alinxalinx/AX7Z020B_2023.1/RSTdocxs/7Z020B_S2_RSTdocument_CN/images/19_media/image26.png

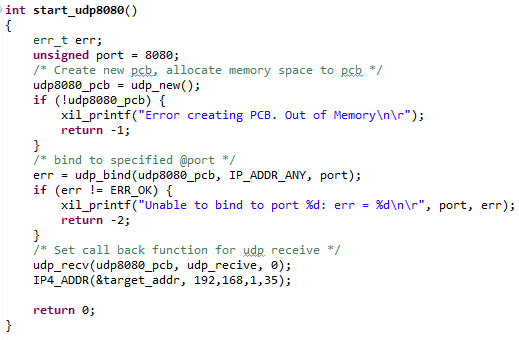
RSTdocxs/7Z020B_S2_RSTdocument_CN/images/19_media/image26.png
