alinxalinx/AX7Z020B_2023.1/RSTdocxs/7Z020B_S3_RSTdocument_CN/images/images0/image1.png

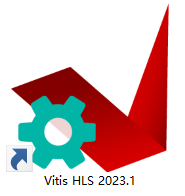
RSTdocxs/7Z020B_S3_RSTdocument_CN/images/images0/image1.png
