alinxalinx/AX7Z020B_2023.1/RSTdocxs/7Z020B_S3_RSTdocument_CN/images/images1/image44.png

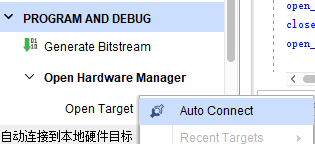
RSTdocxs/7Z020B_S3_RSTdocument_CN/images/images1/image44.png
