alinxalinx/AX7Z020B_2023.1/RSTdocxs/7Z020B_S3_RSTdocument_CN/images/images3/image51.png

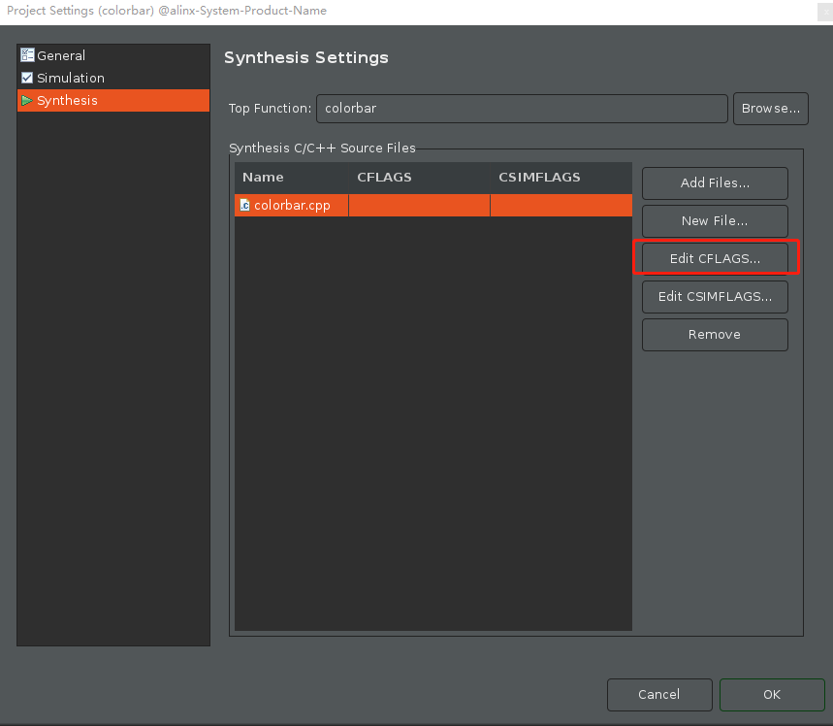
RSTdocxs/7Z020B_S3_RSTdocument_CN/images/images3/image51.png
