alinxalinx/AX7Z020B_2023.1/RSTdocxs/7Z020B_S4_RSTdocument_CN/images/11_media/image39.png

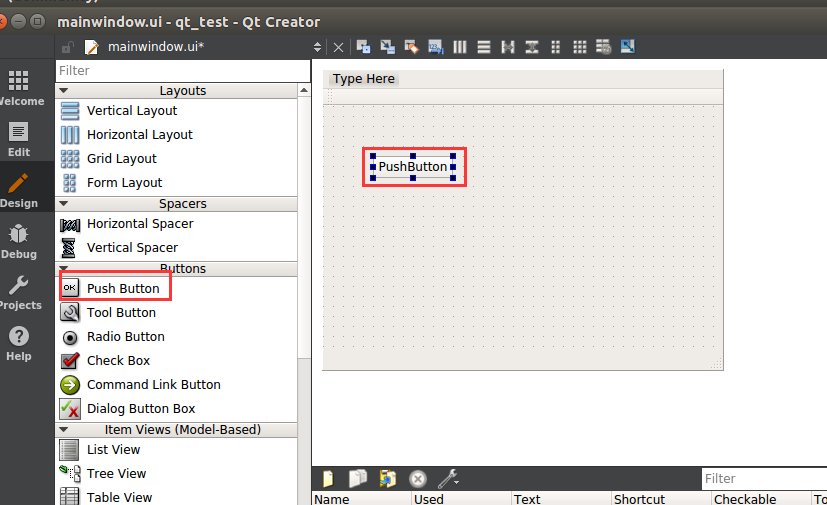
RSTdocxs/7Z020B_S4_RSTdocument_CN/images/11_media/image39.png
