alinxalinx/AX7Z020B_2023.1/course_s4_linux/14_lcd_touch/lcd_touch/Vivado/auto_create_project/src/constraints/lcd7.xdc

set_property PACKAGE_PIN M18 [get_ports lcd_intr]
set_property PACKAGE_PIN M17 [get_ports {lcd_bl_pwm[0]}]
set_property PACKAGE_PIN K19 [get_ports lcd_i2c_scl_io]
set_property PACKAGE_PIN J19 [get_ports lcd_i2c_sda_io]
set_property PACKAGE_PIN B19 [get_ports lcd_hsync]
set_property PACKAGE_PIN A20 [get_ports lcd_vsync]
set_property PACKAGE_PIN B20 [get_ports lcd_dclk]
set_property PACKAGE_PIN C20 [get_ports lcd_de]
set_property PACKAGE_PIN G19 [get_ports {lcd_data[6]}]
set_property PACKAGE_PIN G20 [get_ports {lcd_data[7]}]
set_property PACKAGE_PIN M19 [get_ports {lcd_data[4]}]
set_property PACKAGE_PIN M20 [get_ports {lcd_data[5]}]
set_property PACKAGE_PIN D20 [get_ports {lcd_data[2]}]
set_property PACKAGE_PIN D19 [get_ports {lcd_data[3]}]
set_property PACKAGE_PIN L20 [get_ports {lcd_data[0]}]
set_property PACKAGE_PIN L19 [get_ports {lcd_data[1]}]
set_property PACKAGE_PIN F16 [get_ports {lcd_data[14]}]
set_property PACKAGE_PIN F17 [get_ports {lcd_data[15]}]
set_property PACKAGE_PIN H20 [get_ports {lcd_data[12]}]
set_property PACKAGE_PIN J20 [get_ports {lcd_data[13]}]
set_property PACKAGE_PIN G18 [get_ports {lcd_data[10]}]
set_property PACKAGE_PIN G17 [get_ports {lcd_data[11]}]
set_property PACKAGE_PIN H17 [get_ports {lcd_data[8]}]
set_property PACKAGE_PIN H16 [get_ports {lcd_data[9]}]
set_property PACKAGE_PIN G15 [get_ports {lcd_data[22]}]
set_property PACKAGE_PIN H15 [get_ports {lcd_data[23]}]
set_property PACKAGE_PIN K18 [get_ports {lcd_data[20]}]
set_property PACKAGE_PIN K17 [get_ports {lcd_data[21]}]
set_property PACKAGE_PIN J16 [get_ports {lcd_data[18]}]
set_property PACKAGE_PIN K16 [get_ports {lcd_data[19]}]
set_property PACKAGE_PIN N16 [get_ports {lcd_data[16]}]
set_property PACKAGE_PIN N15 [get_ports {lcd_data[17]}]

set_property IOSTANDARD LVCMOS33 [get_ports lcd_intr]
set_property IOSTANDARD LVCMOS33 [get_ports {lcd_bl_pwm[0]}]
set_property IOSTANDARD LVCMOS33 [get_ports lcd_i2c_scl_io]
set_property IOSTANDARD LVCMOS33 [get_ports lcd_i2c_sda_io]
set_property IOSTANDARD LVCMOS33 [get_ports lcd_hsync]
set_property IOSTANDARD LVCMOS33 [get_ports lcd_vsync]
set_property IOSTANDARD LVCMOS33 [get_ports lcd_dclk]
set_property IOSTANDARD LVCMOS33 [get_ports lcd_de]
set_property IOSTANDARD LVCMOS33 [get_ports {lcd_data[6]}]
set_property IOSTANDARD LVCMOS33 [get_ports {lcd_data[7]}]
set_property IOSTANDARD LVCMOS33 [get_ports {lcd_data[4]}]
set_property IOSTANDARD LVCMOS33 [get_ports {lcd_data[5]}]
set_property IOSTANDARD LVCMOS33 [get_ports {lcd_data[2]}]
set_property IOSTANDARD LVCMOS33 [get_ports {lcd_data[3]}]
set_property IOSTANDARD LVCMOS33 [get_ports {lcd_data[0]}]
set_property IOSTANDARD LVCMOS33 [get_ports {lcd_data[1]}]
set_property IOSTANDARD LVCMOS33 [get_ports {lcd_data[14]}]
set_property IOSTANDARD LVCMOS33 [get_ports {lcd_data[15]}]
set_property IOSTANDARD LVCMOS33 [get_ports {lcd_data[12]}]
set_property IOSTANDARD LVCMOS33 [get_ports {lcd_data[13]}]
set_property IOSTANDARD LVCMOS33 [get_ports {lcd_data[10]}]
set_property IOSTANDARD LVCMOS33 [get_ports {lcd_data[11]}]
set_property IOSTANDARD LVCMOS33 [get_ports {lcd_data[8]}]
set_property IOSTANDARD LVCMOS33 [get_ports {lcd_data[9]}]
set_property IOSTANDARD LVCMOS33 [get_ports {lcd_data[22]}]
set_property IOSTANDARD LVCMOS33 [get_ports {lcd_data[23]}]
set_property IOSTANDARD LVCMOS33 [get_ports {lcd_data[20]}]
set_property IOSTANDARD LVCMOS33 [get_ports {lcd_data[21]}]
set_property IOSTANDARD LVCMOS33 [get_ports {lcd_data[18]}]
set_property IOSTANDARD LVCMOS33 [get_ports {lcd_data[19]}]
set_property IOSTANDARD LVCMOS33 [get_ports {lcd_data[16]}]
set_property IOSTANDARD LVCMOS33 [get_ports {lcd_data[17]}]

set_property PULLUP true [get_ports lcd_i2c_scl_io]
set_property PULLUP true [get_ports lcd_i2c_sda_io]

set_property DRIVE 16 [get_ports {lcd_data[23]}]
set_property DRIVE 16 [get_ports {lcd_data[22]}]
set_property DRIVE 16 [get_ports {lcd_data[21]}]
set_property DRIVE 16 [get_ports {lcd_data[20]}]
set_property DRIVE 16 [get_ports {lcd_data[19]}]
set_property DRIVE 16 [get_ports {lcd_data[18]}]
set_property DRIVE 16 [get_ports {lcd_data[17]}]
set_property DRIVE 16 [get_ports {lcd_data[16]}]
set_property DRIVE 16 [get_ports {lcd_data[15]}]
set_property DRIVE 16 [get_ports {lcd_data[14]}]
set_property DRIVE 16 [get_ports {lcd_data[13]}]
set_property DRIVE 16 [get_ports {lcd_data[12]}]
set_property DRIVE 16 [get_ports {lcd_data[11]}]
set_property DRIVE 16 [get_ports {lcd_data[10]}]
set_property DRIVE 16 [get_ports {lcd_data[9]}]
set_property DRIVE 16 [get_ports {lcd_data[8]}]
set_property DRIVE 16 [get_ports {lcd_data[7]}]
set_property DRIVE 16 [get_ports {lcd_data[6]}]
set_property DRIVE 16 [get_ports {lcd_data[5]}]
set_property DRIVE 16 [get_ports {lcd_data[4]}]
set_property DRIVE 16 [get_ports {lcd_data[3]}]
set_property DRIVE 16 [get_ports {lcd_data[2]}]
set_property DRIVE 16 [get_ports {lcd_data[1]}]
set_property DRIVE 16 [get_ports {lcd_data[0]}]
set_property SLEW FAST [get_ports {lcd_data[23]}]
set_property SLEW FAST [get_ports {lcd_data[22]}]
set_property SLEW FAST [get_ports {lcd_data[21]}]
set_property SLEW FAST [get_ports {lcd_data[20]}]
set_property SLEW FAST [get_ports {lcd_data[19]}]
set_property SLEW FAST [get_ports {lcd_data[18]}]
set_property SLEW FAST [get_ports {lcd_data[17]}]
set_property SLEW FAST [get_ports {lcd_data[16]}]
set_property SLEW FAST [get_ports {lcd_data[15]}]
set_property SLEW FAST [get_ports {lcd_data[14]}]
set_property SLEW FAST [get_ports {lcd_data[13]}]
set_property SLEW FAST [get_ports {lcd_data[12]}]
set_property SLEW FAST [get_ports {lcd_data[11]}]
set_property SLEW FAST [get_ports {lcd_data[10]}]
set_property SLEW FAST [get_ports {lcd_data[9]}]
set_property SLEW FAST [get_ports {lcd_data[8]}]
set_property SLEW FAST [get_ports {lcd_data[7]}]
set_property SLEW FAST [get_ports {lcd_data[6]}]
set_property SLEW FAST [get_ports {lcd_data[5]}]
set_property SLEW FAST [get_ports {lcd_data[4]}]
set_property SLEW FAST [get_ports {lcd_data[3]}]
set_property SLEW FAST [get_ports {lcd_data[2]}]
set_property SLEW FAST [get_ports {lcd_data[1]}]
set_property SLEW FAST [get_ports {lcd_data[0]}]
set_property DRIVE 16 [get_ports lcd_de]
set_property DRIVE 16 [get_ports lcd_hsync]
set_property DRIVE 16 [get_ports lcd_vsync]
set_property DRIVE 16 [get_ports {lcd_bl_pwm[0]}]
set_property SLEW FAST [get_ports lcd_de]
set_property SLEW FAST [get_ports lcd_hsync]
set_property SLEW FAST [get_ports lcd_vsync]
set_property SLEW FAST [get_ports {lcd_bl_pwm[0]}]
set_property DRIVE 16 [get_ports lcd_dclk]
set_property SLEW FAST [get_ports lcd_dclk]
