alinxalinx/AX7Z020B_2023.1/course_s1_fpga/01_led/auto_create_project/src/constraints/led.xdc

set_property PACKAGE_PIN H18 [get_ports {led[3]}]
set_property PACKAGE_PIN J18 [get_ports {led[2]}]
set_property PACKAGE_PIN K14 [get_ports {led[1]}]
set_property PACKAGE_PIN J14 [get_ports {led[0]}]
set_property PACKAGE_PIN M15 [get_ports rst_n]
set_property PACKAGE_PIN U18 [get_ports sys_clk]
set_property IOSTANDARD LVCMOS33 [get_ports {led[3]}]
set_property IOSTANDARD LVCMOS33 [get_ports {led[2]}]
set_property IOSTANDARD LVCMOS33 [get_ports {led[1]}]
set_property IOSTANDARD LVCMOS33 [get_ports {led[0]}]
set_property IOSTANDARD LVCMOS33 [get_ports rst_n]
set_property IOSTANDARD LVCMOS33 [get_ports sys_clk]

create_clock -period 20.000 -name sys_clk -waveform {0.000 10.000} [get_ports sys_clk]

create_debug_core u_ila_0 ila
set_property ALL_PROBE_SAME_MU true [get_debug_cores u_ila_0]
set_property ALL_PROBE_SAME_MU_CNT 1 [get_debug_cores u_ila_0]
set_property C_ADV_TRIGGER false [get_debug_cores u_ila_0]
set_property C_DATA_DEPTH 1024 [get_debug_cores u_ila_0]
set_property C_EN_STRG_QUAL false [get_debug_cores u_ila_0]
set_property C_INPUT_PIPE_STAGES 0 [get_debug_cores u_ila_0]
set_property C_TRIGIN_EN false [get_debug_cores u_ila_0]
set_property C_TRIGOUT_EN false [get_debug_cores u_ila_0]
set_property port_width 1 [get_debug_ports u_ila_0/clk]
connect_debug_port u_ila_0/clk [get_nets [list sys_clk_IBUF_BUFG]]
set_property PROBE_TYPE DATA_AND_TRIGGER [get_debug_ports u_ila_0/probe0]
set_property port_width 4 [get_debug_ports u_ila_0/probe0]
connect_debug_port u_ila_0/probe0 [get_nets [list {led_OBUF[0]} {led_OBUF[1]} {led_OBUF[2]} {led_OBUF[3]}]]
create_debug_port u_ila_0 probe
set_property PROBE_TYPE DATA_AND_TRIGGER [get_debug_ports u_ila_0/probe1]
set_property port_width 32 [get_debug_ports u_ila_0/probe1]
connect_debug_port u_ila_0/probe1 [get_nets [list {timer_cnt[0]} {timer_cnt[1]} {timer_cnt[2]} {timer_cnt[3]} {timer_cnt[4]} {timer_cnt[5]} {timer_cnt[6]} {timer_cnt[7]} {timer_cnt[8]} {timer_cnt[9]} {timer_cnt[10]} {timer_cnt[11]} {timer_cnt[12]} {timer_cnt[13]} {timer_cnt[14]} {timer_cnt[15]} {timer_cnt[16]} {timer_cnt[17]} {timer_cnt[18]} {timer_cnt[19]} {timer_cnt[20]} {timer_cnt[21]} {timer_cnt[22]} {timer_cnt[23]} {timer_cnt[24]} {timer_cnt[25]} {timer_cnt[26]} {timer_cnt[27]} {timer_cnt[28]} {timer_cnt[29]} {timer_cnt[30]} {timer_cnt[31]}]]
set_property C_CLK_INPUT_FREQ_HZ 300000000 [get_debug_cores dbg_hub]
set_property C_ENABLE_CLK_DIVIDER false [get_debug_cores dbg_hub]
set_property C_USER_SCAN_CHAIN 1 [get_debug_cores dbg_hub]
connect_debug_port dbg_hub/clk [get_nets sys_clk_IBUF_BUFG]
