alinxalinx/AX7Z020B_2023.1/course_s2_vitis/14_ad7606_dma_hdmi/Vivado/auto_create_project/src/constraints/ad7606.xdc

set_property PACKAGE_PIN M18 [get_ports {ADC_PORT_ad7606_os[1]}]
set_property PACKAGE_PIN M17 [get_ports {ADC_PORT_ad7606_os[0]}]
set_property PACKAGE_PIN K19 [get_ports  ADC_PORT_ad7606_convstab]
set_property PACKAGE_PIN J19 [get_ports {ADC_PORT_ad7606_os[2]}]
set_property PACKAGE_PIN B19 [get_ports  ADC_PORT_ad7606_rd]
set_property PACKAGE_PIN A20 [get_ports  ADC_PORT_ad7606_reset]
set_property PACKAGE_PIN B20 [get_ports  ADC_PORT_ad7606_busy]
set_property PACKAGE_PIN C20 [get_ports  ADC_PORT_ad7606_cs]
set_property PACKAGE_PIN G20 [get_ports  ADC_PORT_ad7606_first_data]
set_property PACKAGE_PIN D20 [get_ports {ADC_PORT_ad7606_data[0]}]
set_property PACKAGE_PIN D19 [get_ports {ADC_PORT_ad7606_data[1]}]
set_property PACKAGE_PIN L20 [get_ports {ADC_PORT_ad7606_data[2]}]
set_property PACKAGE_PIN L19 [get_ports {ADC_PORT_ad7606_data[3]}]
set_property PACKAGE_PIN F16 [get_ports {ADC_PORT_ad7606_data[4]}]
set_property PACKAGE_PIN F17 [get_ports {ADC_PORT_ad7606_data[5]}]
set_property PACKAGE_PIN H20 [get_ports {ADC_PORT_ad7606_data[6]}]
set_property PACKAGE_PIN J20 [get_ports {ADC_PORT_ad7606_data[7]}]
set_property PACKAGE_PIN G18 [get_ports {ADC_PORT_ad7606_data[8]}]
set_property PACKAGE_PIN G17 [get_ports {ADC_PORT_ad7606_data[9]}]
set_property PACKAGE_PIN H17 [get_ports {ADC_PORT_ad7606_data[10]}]
set_property PACKAGE_PIN H16 [get_ports {ADC_PORT_ad7606_data[11]}]
set_property PACKAGE_PIN G15 [get_ports {ADC_PORT_ad7606_data[12]}]
set_property PACKAGE_PIN H15 [get_ports {ADC_PORT_ad7606_data[13]}]
set_property PACKAGE_PIN K18 [get_ports {ADC_PORT_ad7606_data[14]}]
set_property PACKAGE_PIN K17 [get_ports {ADC_PORT_ad7606_data[15]}]



set_property IOSTANDARD LVCMOS33 [get_ports ADC_PORT_ad7606_convstab]
set_property IOSTANDARD LVCMOS33 [get_ports ADC_PORT_ad7606_reset]
set_property IOSTANDARD LVCMOS33 [get_ports ADC_PORT_ad7606_rd]
set_property IOSTANDARD LVCMOS33 [get_ports ADC_PORT_ad7606_cs]
set_property IOSTANDARD LVCMOS33 [get_ports ADC_PORT_ad7606_busy]
set_property IOSTANDARD LVCMOS33 [get_ports ADC_PORT_ad7606_first_data]
set_property IOSTANDARD LVCMOS33 [get_ports {ADC_PORT_ad7606_os[*]}]
set_property IOSTANDARD LVCMOS33 [get_ports {ADC_PORT_ad7606_data[*]}]
