alinxalinx/AX7Z020B_2023.1/course_s2_vitis/12_ad9280_dma_hdmi/Vivado/auto_create_project/src/constraints/ad9280.xdc

set_property PACKAGE_PIN K18 [get_ports adc_clk]
set_property PACKAGE_PIN H20 [get_ports {adc_data[0]}]
set_property PACKAGE_PIN J20 [get_ports {adc_data[1]}]
set_property PACKAGE_PIN G18 [get_ports {adc_data[2]}]
set_property PACKAGE_PIN G17 [get_ports {adc_data[3]}]
set_property PACKAGE_PIN H17 [get_ports {adc_data[4]}]
set_property PACKAGE_PIN H16 [get_ports {adc_data[5]}]
set_property PACKAGE_PIN G15 [get_ports {adc_data[6]}]
set_property PACKAGE_PIN H15 [get_ports {adc_data[7]}]


set_property IOSTANDARD LVCMOS33 [get_ports adc_clk]
set_property IOSTANDARD LVCMOS33 [get_ports {adc_data[*]}]
