alinxalinx/AX7Z020B_2023.1/course_s2_vitis/22_an5641_mipi_hdmi/Vivado/auto_create_project/src/constraints/mipi.xdc

set_property PACKAGE_PIN U7 [get_ports {cam_gpio_tri_io[0]}]
set_property IOSTANDARD LVCMOS33 [get_ports {cam_gpio_tri_io[0]}]
set_property PULLUP true [get_ports {cam_gpio_tri_io[0]}]

set_property -dict {PACKAGE_PIN T5 IOSTANDARD LVCMOS33} [get_ports cam_i2c_scl_io]
set_property -dict {PACKAGE_PIN U5 IOSTANDARD LVCMOS33} [get_ports cam_i2c_sda_io]

set_property PULLUP true [get_ports cam_i2c_scl_io]
set_property PULLUP true [get_ports cam_i2c_sda_io]

set_property INTERNAL_VREF 0.6 [get_iobanks 13]

set_property -dict {PACKAGE_PIN W8 IOSTANDARD HSUL_12} [get_ports mipi_phy_if_clk_lp_n]
set_property -dict {PACKAGE_PIN V8 IOSTANDARD HSUL_12} [get_ports mipi_phy_if_clk_lp_p]

set_property -dict {PACKAGE_PIN U10 IOSTANDARD HSUL_12} [get_ports {mipi_phy_if_data_lp_n[0]}]
set_property -dict {PACKAGE_PIN T9 IOSTANDARD HSUL_12} [get_ports {mipi_phy_if_data_lp_p[0]}]
set_property -dict {PACKAGE_PIN Y13 IOSTANDARD HSUL_12} [get_ports {mipi_phy_if_data_lp_n[1]}]
set_property -dict {PACKAGE_PIN Y12 IOSTANDARD HSUL_12} [get_ports {mipi_phy_if_data_lp_p[1]}]

set_property -dict {PACKAGE_PIN Y6 IOSTANDARD LVDS_25} [get_ports mipi_phy_if_clk_hs_n]
set_property -dict {PACKAGE_PIN Y7 IOSTANDARD LVDS_25} [get_ports mipi_phy_if_clk_hs_p]


set_property -dict {PACKAGE_PIN Y11 IOSTANDARD LVDS_25} [get_ports {mipi_phy_if_data_hs_n[0]}]
set_property -dict {PACKAGE_PIN W11 IOSTANDARD LVDS_25} [get_ports {mipi_phy_if_data_hs_p[0]}]
set_property -dict {PACKAGE_PIN U8 IOSTANDARD LVDS_25} [get_ports {mipi_phy_if_data_hs_n[1]}]
set_property -dict {PACKAGE_PIN U9 IOSTANDARD LVDS_25} [get_ports {mipi_phy_if_data_hs_p[1]}]
