alinxalinx/AX7Z020B_2023.1/course_s2_vitis/02_ps_xadc/Vivado/auto_create_project/src/constraints/xadc.xdc

set_property PACKAGE_PIN E17 [get_ports Vaux1_v_p]
set_property IOSTANDARD LVCMOS33 [get_ports Vaux1_v_n]
set_property IOSTANDARD LVCMOS33 [get_ports Vaux1_v_p]
set_property IOSTANDARD LVCMOS33 [get_ports Vaux9_v_n]
set_property IOSTANDARD LVCMOS33 [get_ports Vaux9_v_p]
set_property IOSTANDARD LVCMOS33 [get_ports Vaux12_v_n]
set_property IOSTANDARD LVCMOS33 [get_ports Vaux12_v_p]
