alinxalinx/AX7Z020B_2023.1/course_s2_vitis/08_dualcore_amp/Vivado/auto_create_project/src/constraints/led.xdc

#LED2
set_property IOSTANDARD LVCMOS33 [get_ports {led_tri_o[0]}]
set_property PACKAGE_PIN K14 [get_ports {led_tri_o[0]}]
#KEY2
set_property IOSTANDARD LVCMOS33 [get_ports {key_tri_i[0]}]
set_property PACKAGE_PIN M14 [get_ports {key_tri_i[0]}]
#LED1
set_property IOSTANDARD LVCMOS33 [get_ports {GPIO_tri_io[0]}]
set_property PACKAGE_PIN J14 [get_ports {GPIO_tri_io[0]}]
#KEY1
set_property IOSTANDARD LVCMOS33 [get_ports {GPIO_tri_io[1]}]
set_property PACKAGE_PIN M15 [get_ports {GPIO_tri_io[1]}]
