alinxalinx/AX7Z020B_2023.1/course_s2_vitis/22_an5641_mipi_hdmi/Vivado/auto_create_project/src/constraints/system.xdc

set_property BITSTREAM.GENERAL.COMPRESS TRUE [current_design]

#LED
set_property IOSTANDARD LVCMOS33 [get_ports {leds_tri_o[0]}]
set_property PACKAGE_PIN J14 [get_ports {leds_tri_o[0]}]
set_property IOSTANDARD LVCMOS33 [get_ports {leds_tri_o[1]}]
set_property PACKAGE_PIN K14 [get_ports {leds_tri_o[1]}]
