alinxalinx/AX7Z020B_2023.1/course_s2_vitis/22_an5641_mipi_hdmi/Vitis/auto_create_vitis/src/mipi_hdmi/vdma.c

#include "xil_printf.h"
#include "vdma.h"

u32 vdma_version(XAxiVdma *Vdma) {
	return XAxiVdma_GetVersion(Vdma);
}

int vdma_read_start(XAxiVdma *Vdma) {
	int Status;

	// MM2S Startup
	Status = XAxiVdma_DmaStart(Vdma, XAXIVDMA_READ);
	if (Status != XST_SUCCESS)
	{
	   xil_printf("Start read transfer failed %d\n\r", Status);
	   return XST_FAILURE;
	}

	return XST_SUCCESS;
}


int vdma_read_stop(XAxiVdma *Vdma) {
	XAxiVdma_DmaStop(Vdma, XAXIVDMA_READ);
	return XST_SUCCESS;
}


int vdma_read_init(short DeviceID,short HoriSizeInput,short VertSizeInput,short Stride,unsigned int FrameStoreStartAddr)
{
	XAxiVdma Vdma;
	XAxiVdma_Config *Config;
	XAxiVdma_DmaSetup ReadCfg;
	int Status;


	Config = XAxiVdma_LookupConfig(DeviceID);
	if (NULL == Config) {
		xil_printf("XAxiVdma_LookupConfig failure\r\n");
		return XST_FAILURE;
	}

	Status = XAxiVdma_CfgInitialize(&Vdma, Config, Config->BaseAddress);
	if (Status != XST_SUCCESS) {
		xil_printf("XAxiVdma_CfgInitialize failure\r\n");
		return XST_FAILURE;
	}

	

	ReadCfg.EnableCircularBuf = 1;
	ReadCfg.EnableFrameCounter = 0;
	ReadCfg.FixedFrameStoreAddr = 0;

	ReadCfg.EnableSync = 1;
	ReadCfg.PointNum = 1;

	ReadCfg.FrameDelay = 0;

	ReadCfg.VertSizeInput = VertSizeInput;
	ReadCfg.HoriSizeInput = HoriSizeInput;
	ReadCfg.Stride = Stride;

	Status = XAxiVdma_DmaConfig(&Vdma, XAXIVDMA_READ, &ReadCfg);
	if (Status != XST_SUCCESS) {
			xdbg_printf(XDBG_DEBUG_ERROR,
				"Read channel config failed %d\r\n", Status);

			return XST_FAILURE;
	}


	ReadCfg.FrameStoreStartAddr[0] = FrameStoreStartAddr;

	Status = XAxiVdma_DmaSetBufferAddr(&Vdma, XAXIVDMA_READ, ReadCfg.FrameStoreStartAddr);
	if (Status != XST_SUCCESS) {
			xdbg_printf(XDBG_DEBUG_ERROR,"Read channel set buffer address failed %d\r\n", Status);
			return XST_FAILURE;
	}


	Status = vdma_read_start(&Vdma);
	if (Status != XST_SUCCESS) {
		   xil_printf("error starting VDMA..!");
		   return Status;
	}
	return XST_SUCCESS;

}


int vdma_write_start(XAxiVdma *Vdma) {
	int Status;

	// MM2S Startup
	Status = XAxiVdma_DmaStart(Vdma, XAXIVDMA_WRITE);
	if (Status != XST_SUCCESS)
	{
	   xil_printf("Start write transfer failed %d\n\r", Status);
	   return XST_FAILURE;
	}

	return XST_SUCCESS;
}


int vdma_write_stop(XAxiVdma *Vdma) {
	XAxiVdma_DmaStop(Vdma, XAXIVDMA_WRITE);
	return XST_SUCCESS;
}


int vdma_write_init(short DeviceID,short HoriSizeInput,short VertSizeInput,short Stride,unsigned int FrameStoreStartAddr)
{
	XAxiVdma Vdma;
	XAxiVdma_Config *Config;
	XAxiVdma_DmaSetup WriteCfg;
	int Status;


	Config = XAxiVdma_LookupConfig(DeviceID);
	if (NULL == Config) {
		xil_printf("XAxiVdma_LookupConfig failure\r\n");
		return XST_FAILURE;
	}

	Status = XAxiVdma_CfgInitialize(&Vdma, Config, Config->BaseAddress);
	if (Status != XST_SUCCESS) {
		xil_printf("XAxiVdma_CfgInitialize failure\r\n");
		return XST_FAILURE;
	}

	

	WriteCfg.EnableCircularBuf = 0;
	WriteCfg.EnableFrameCounter = 0;
	WriteCfg.FixedFrameStoreAddr = 0;

	WriteCfg.EnableSync = 1;
	WriteCfg.PointNum = 1;

	WriteCfg.FrameDelay = 0;

	WriteCfg.VertSizeInput = VertSizeInput;
	WriteCfg.HoriSizeInput = HoriSizeInput;
	WriteCfg.Stride = Stride;

	Status = XAxiVdma_DmaConfig(&Vdma, XAXIVDMA_WRITE, &WriteCfg);
	if (Status != XST_SUCCESS) {
			xdbg_printf(XDBG_DEBUG_ERROR,
				"Read channel config failed %d\r\n", Status);

			return XST_FAILURE;
	}


	WriteCfg.FrameStoreStartAddr[0] = FrameStoreStartAddr;

	Status = XAxiVdma_DmaSetBufferAddr(&Vdma, XAXIVDMA_WRITE, WriteCfg.FrameStoreStartAddr);
	if (Status != XST_SUCCESS) {
			xdbg_printf(XDBG_DEBUG_ERROR,"Write channel set buffer address failed %d\r\n", Status);
			return XST_FAILURE;
	}


	Status = vdma_write_start(&Vdma);
	if (Status != XST_SUCCESS) {
		   xil_printf("error starting VDMA..!");
		   return Status;
	}
	return XST_SUCCESS;

}
