alinxalinx/AX7Z020B_2023.1/course_s2_vitis/03_i2c_test/Vitis/auto_create_vitis/src/temp_test/i2c/PS_i2c.h

#ifndef __PS_I2C_H__
#define __PS_I2C_H__

#include "xil_types.h"
#include "xiicps.h"

int i2c_reg8_write(XIicPs *InstancePtr, char IIC_ADDR, char Addr, char Data);
char i2c_reg8_read(XIicPs *InstancePtr, char IIC_ADDR, s32 ByteCount, char Addr);
int i2c_reg16_write(XIicPs *InstancePtr, char IIC_ADDR, unsigned short Addr, char Data);
char i2c_reg16_read(XIicPs *InstancePtr, char IIC_ADDR, unsigned short Addr);
int i2c_init(XIicPs *Iic,short DeviceID ,u32 IIC_SCLK_RATE);

#endif
